ojthetiny/OpenTKL/PCB/Kicad Files/UniversalTKL.kicad_sch

## KiCad design PCB/Kicad Files/UniversalTKL.kicad_sch (2021-07-17)

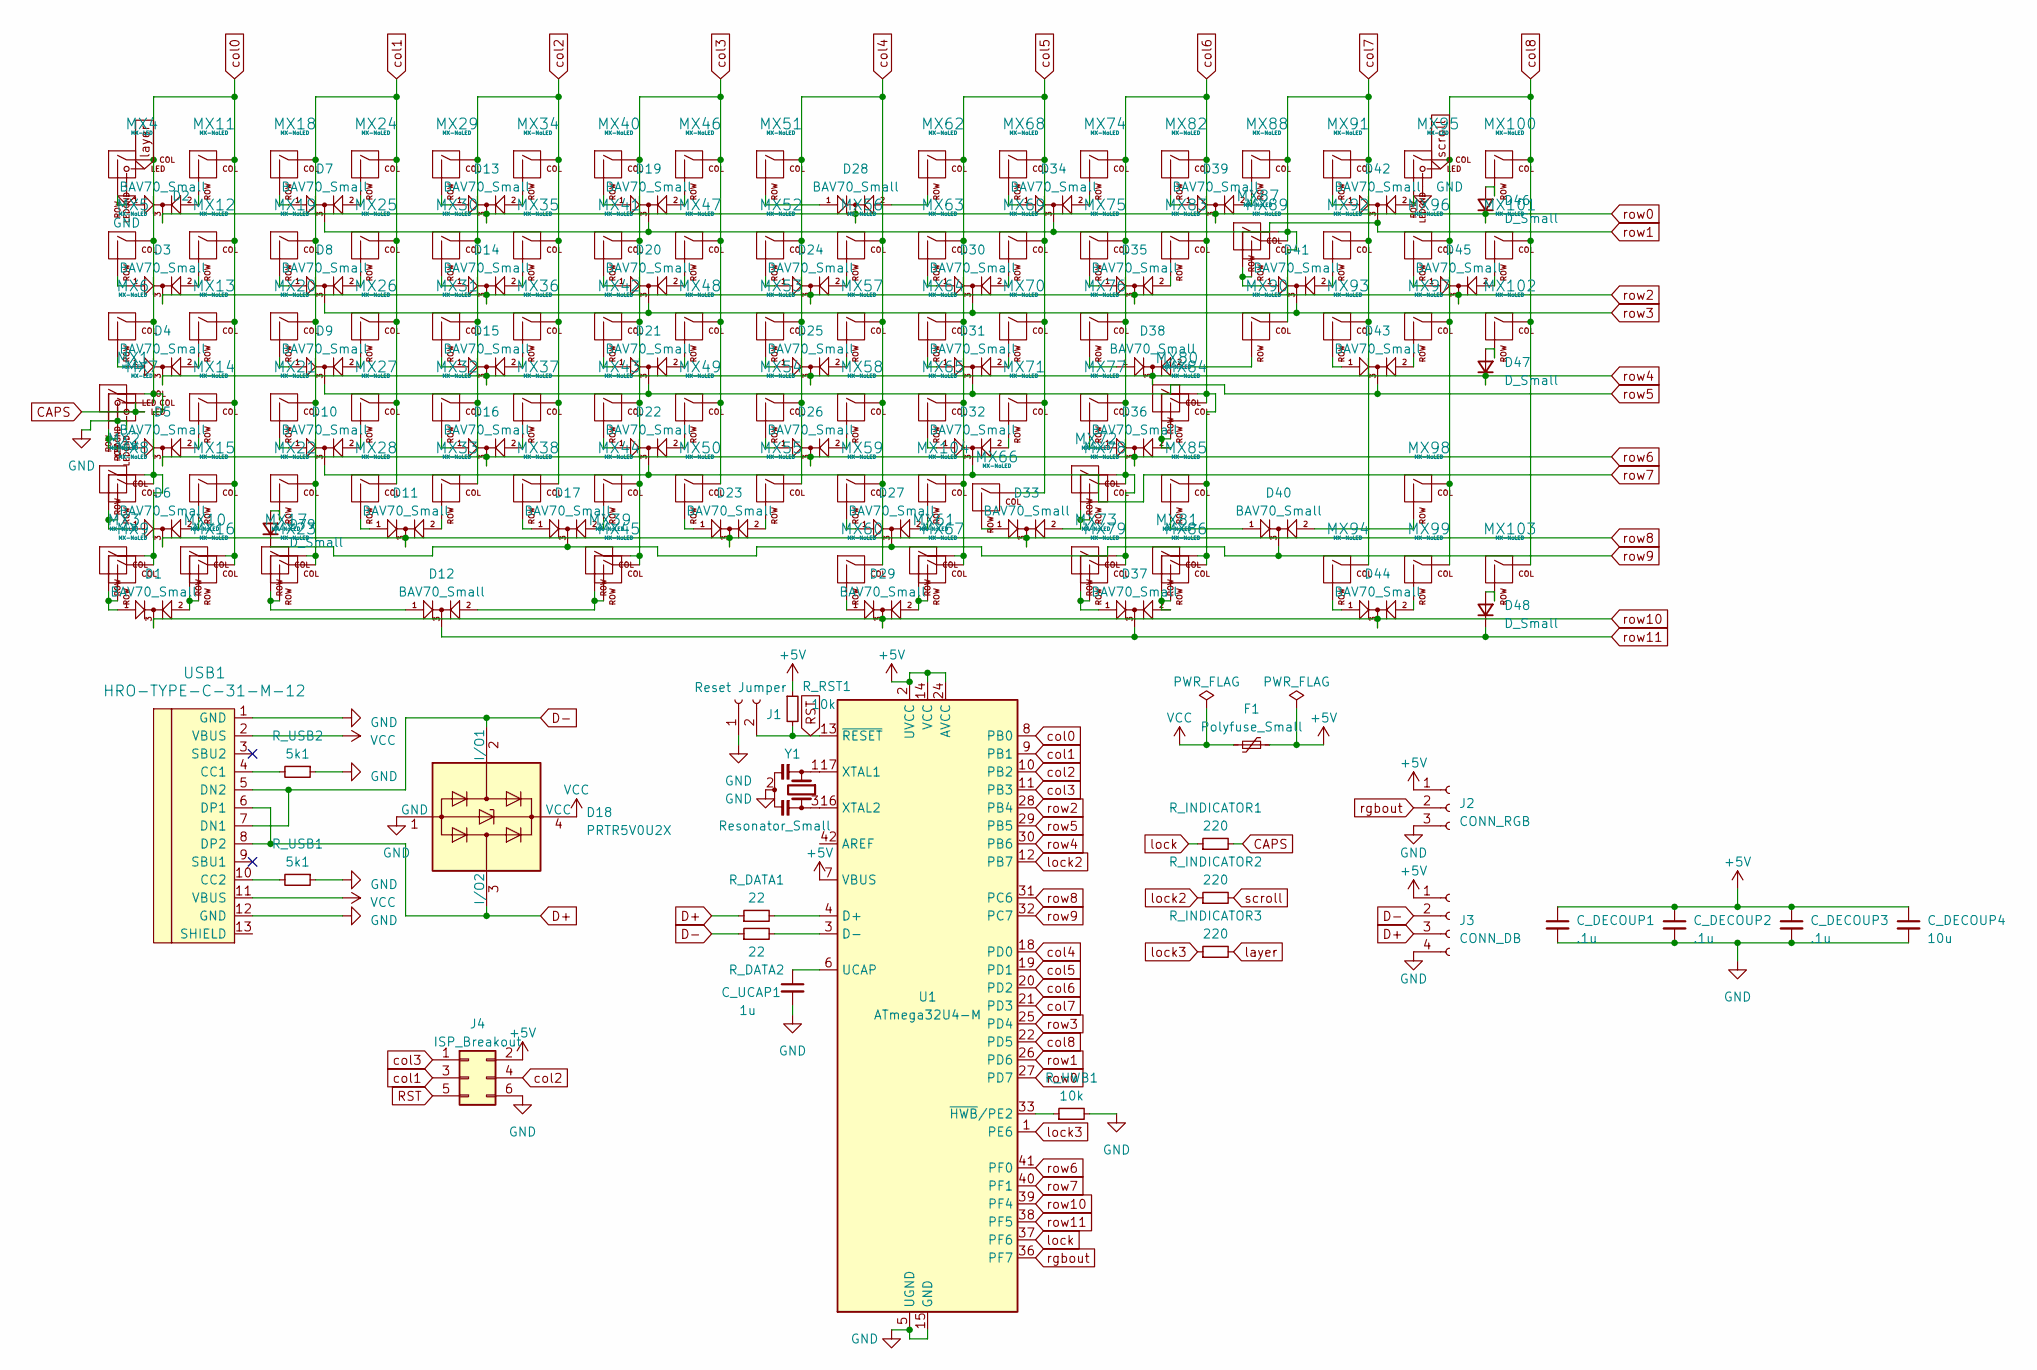
[picture p6: schematic UniversalTKL.kicad_sch]

Parts:
C_DECOUP1, C_DECOUP2, C_DECOUP3: .1u; C_0402_1005Metric
C_DECOUP4: 10u; C_0402_1005Metric
C_UCAP1: 1u; C_0402_1005Metric
D1, D2, D3, D4, D5, D6, D7, D8, D9, D10, D11, D12, D13, D14, D15, D16, D17, D19, D20, D21, D22, D23, D24, D25, D26, D27, D28, D29, D30, D31, D32, D33, D34, D35, D36, D37, D38, D39, D40, D41, D42, D43, D44, D45: BAV70_Small; SOT-23
D18: PRTR5V0U2X; SOT-143
D46, D47, D48, D79: D_Small; D_SOD-123
F1: Polyfuse_Small; Fuse_0805_2012Metric
J1: Reset Jumper; SW_SPST_TL3342
J2: CONN_RGB; PinHeader_1x03_P2.54mm_Vertical
J3: CONN_DB; JST_SH_SM04B-SRSS-TB_1x04-1MP_P1.00mm_Horizontal
J4: ISP_Breakout; PinHeader_2x03_P2.54mm_Vertical
MX1: MX-LED; MX-1.25U
MX2, MX3, MX10, MX17, MX60, MX61, MX73, MX81: MX-NoLED; MX-1.25U-NoLED
MX4, MX95: MX-LED; MX-1U
MX5, MX11, MX12, MX13, MX14, MX15, MX16, MX18, MX19, MX20, MX21, MX22, MX24, MX25, MX26, MX27, MX28, MX29, MX30, MX31, MX32, MX33, MX34, MX35, MX36, MX37, MX38, MX40, MX41, MX42, MX43, MX44, MX46, MX47, MX48, MX49, MX50, MX51, MX52, MX53, MX54, MX55, MX56, MX57, MX58, MX59, MX62, MX63, MX64, MX65, MX66, MX68, MX69, MX70, MX71, MX74, MX75, MX76, MX77, MX79, MX82, MX83, MX85, MX87, MX88, MX91, MX92, MX93, MX94, MX96, MX97, MX98, MX99, MX100, MX101, MX102, MX103, MX104: MX-NoLED; MX-1U-NoLED
MX6, MX9, MX23, MX67, MX86, MX90: MX-NoLED; MX-1.5U-NoLED
MX7: MX-LED; MX-1.75U
MX8: MX-NoLED; MX-2.25U-NoLED
MX39: MX-NoLED; MX-6.25U-ReversedStabilizers-NoLED
MX45: MX-NoLED; MX-7U-ReversedStabilizers-NoLED
MX72: MX-NoLED; MX-2.75U-NoLED
MX78: MX-NoLED; MX-1.75U_NoLED
MX80: MX-NoLED; MX-ISO-ReversedStabilizers
MX84: MX-NoLED; MX-2.25U-ReversedStabilizers-NoLED
MX89: MX-NoLED; MX-2U-NoLED
R_DATA1, R_DATA2: 22; R_0402_1005Metric
R_HWB1: 10k; R_0402_1005Metric
R_INDICATOR1, R_INDICATOR2, R_INDICATOR3: 220; R_0402_1005Metric
R_RST1: 10k; R_0402_1005Metric
R_USB1, R_USB2: 5k1; R_0402_1005Metric
U1: ATmega32U4-M; QFN-44-1EP_7x7mm_P0.5mm_EP5.2x5.2mm
USB1: HRO-TYPE-C-31-M-12; HRO-TYPE-C-31-M-12-Assembly
Y1: Resonator_Small; Resonator_SMD_Murata_CSTxExxV-3Pin_3.0x1.1mm

Connections:
+5V: C_DECOUP1.1, C_DECOUP2.1, C_DECOUP3.1, C_DECOUP4.1, F1.2, J2.1, J3.1, J4.2, R_RST1.1, U1.2 (UVCC), U1.7 (VBUS), U1.14 (VCC), U1.24 (AVCC), U1.34 (VCC), U1.44 (AVCC)
CAPS: MX1.3 (LED), MX7.3 (LED), R_INDICATOR1.2
D+: D18.3 (I/O2), J3.3, R_DATA1.1, USB1.6 (DP1), USB1.8 (DP2)
D-: D18.2 (I/O1), J3.2, R_DATA2.1, USB1.5 (DN2), USB1.7 (DN1)
GND: C_DECOUP1.2, C_DECOUP2.2, C_DECOUP3.2, C_DECOUP4.2, C_UCAP1.2, D18.1 (GND), J1.1, J2.3, J3.4, J4.6, MX1.4 (LEDGND), MX4.4 (LEDGND), MX7.4 (LEDGND), MX95.4 (LEDGND), R_HWB1.2, R_USB1.1, R_USB2.1, U1.5 (UGND), U1.15 (GND), U1.23 (GND), U1.35 (GND), U1.43 (GND), U1.45 (GND), USB1.1 (GND), USB1.12 (GND), Y1.2
unnamed: C_UCAP1.1, U1.6 (UCAP)
unnamed: D1.1 (A1), MX3.2 (ROW), MX9.2 (ROW)
unnamed: D1.2 (A2), MX10.2 (ROW), MX16.2 (ROW)
unnamed: D2.1 (A1), MX4.2 (ROW)
unnamed: D2.2 (A2), MX11.2 (ROW)
unnamed: D3.1 (A1), MX5.2 (ROW)
unnamed: D3.2 (A2), MX12.2 (ROW)
unnamed: D4.1 (A1), MX6.2 (ROW)
unnamed: D4.2 (A2), MX13.2 (ROW)
unnamed: D5.1 (A1), MX1.2 (ROW), MX7.2 (ROW)
unnamed: D5.2 (A2), MX14.2 (ROW)
unnamed: D6.1 (A1), MX2.2 (ROW), MX8.2 (ROW)
unnamed: D6.2 (A2), MX15.2 (ROW)
unnamed: D7.1 (A1), MX18.2 (ROW)
unnamed: D7.2 (A2), MX24.2 (ROW)
unnamed: D8.1 (A1), MX19.2 (ROW)
unnamed: D8.2 (A2), MX25.2 (ROW)
unnamed: D9.1 (A1), MX20.2 (ROW)
unnamed: D9.2 (A2), MX26.2 (ROW)
unnamed: D10.1 (A1), MX21.2 (ROW)
unnamed: D10.2 (A2), MX27.2 (ROW)
unnamed: D11.1 (A1), MX28.2 (ROW)
unnamed: D11.2 (A2), MX33.2 (ROW)
unnamed: D12.1 (A1), MX17.2 (ROW), MX23.2 (ROW)
unnamed: D12.2 (A2), MX39.2 (ROW), MX45.2 (ROW)
unnamed: D13.1 (A1), MX29.2 (ROW)
unnamed: D13.2 (A2), MX34.2 (ROW)
unnamed: D14.1 (A1), MX30.2 (ROW)
unnamed: D14.2 (A2), MX35.2 (ROW)
unnamed: D15.1 (A1), MX31.2 (ROW)
unnamed: D15.2 (A2), MX36.2 (ROW)
unnamed: D16.1 (A1), MX32.2 (ROW)
unnamed: D16.2 (A2), MX37.2 (ROW)
unnamed: D17.1 (A1), MX38.2 (ROW)
unnamed: D17.2 (A2), MX44.2 (ROW)
unnamed: D19.1 (A1), MX40.2 (ROW)
unnamed: D19.2 (A2), MX46.2 (ROW)
unnamed: D20.1 (A1), MX41.2 (ROW)
unnamed: D20.2 (A2), MX47.2 (ROW)
unnamed: D21.1 (A1), MX42.2 (ROW)
unnamed: D21.2 (A2), MX48.2 (ROW)
unnamed: D22.1 (A1), MX43.2 (ROW)
unnamed: D22.2 (A2), MX49.2 (ROW)
unnamed: D23.1 (A1), MX50.2 (ROW)
unnamed: D23.2 (A2), MX55.2 (ROW)
unnamed: D24.1 (A1), MX52.2 (ROW)
unnamed: D24.2 (A2), MX56.2 (ROW)
unnamed: D25.1 (A1), MX53.2 (ROW)
unnamed: D25.2 (A2), MX57.2 (ROW)
unnamed: D26.1 (A1), MX54.2 (ROW)
unnamed: D26.2 (A2), MX58.2 (ROW)
unnamed: D27.1 (A1), MX59.2 (ROW)
unnamed: D27.2 (A2), MX104.2 (ROW)
unnamed: D28.1 (A1), MX51.2 (ROW)
unnamed: D28.2 (A2), MX62.2 (ROW)
unnamed: D29.1 (A1), MX60.2 (ROW)
unnamed: D29.2 (A2), MX61.2 (ROW), MX67.2 (ROW)
unnamed: D30.1 (A1), MX63.2 (ROW)
unnamed: D30.2 (A2), MX69.2 (ROW)
unnamed: D31.1 (A1), MX64.2 (ROW)
unnamed: D31.2 (A2), MX70.2 (ROW)
unnamed: D32.1 (A1), MX65.2 (ROW)
unnamed: D32.2 (A2), MX71.2 (ROW)
unnamed: D33.1 (A1), MX66.2 (ROW)
unnamed: D33.2 (A2), MX72.2 (ROW), MX78.2 (ROW)
unnamed: D34.1 (A1), MX68.2 (ROW)
unnamed: D34.2 (A2), MX74.2 (ROW)
unnamed: D35.1 (A1), MX75.2 (ROW)
unnamed: D35.2 (A2), MX83.2 (ROW)
unnamed: D36.1 (A1), MX77.2 (ROW)
unnamed: D36.2 (A2), MX80.2 (ROW), MX84.2 (ROW)
unnamed: D37.1 (A1), MX73.2 (ROW), MX79.2 (ROW)
unnamed: D37.2 (A2), MX81.2 (ROW), MX86.2 (ROW)
unnamed: D38.1 (A1), MX76.2 (ROW)
unnamed: D38.2 (A2), MX90.2 (ROW)
unnamed: D39.1 (A1), MX82.2 (ROW)
unnamed: D39.2 (A2), MX88.2 (ROW)
unnamed: D40.1 (A1), MX85.2 (ROW)
unnamed: D40.2 (A2), MX98.2 (ROW)
unnamed: D41.1 (A1), MX87.2 (ROW), MX89.2 (ROW)
unnamed: D41.2 (A2), MX92.2 (ROW)
unnamed: D42.1 (A1), MX91.2 (ROW)
unnamed: D42.2 (A2), MX95.2 (ROW)
unnamed: D43.1 (A1), MX93.2 (ROW)
unnamed: D43.2 (A2), MX97.2 (ROW)
unnamed: D44.1 (A1), MX94.2 (ROW)
unnamed: D44.2 (A2), MX99.2 (ROW)
unnamed: D45.1 (A1), MX96.2 (ROW)
unnamed: D45.2 (A2), MX101.2 (ROW)
unnamed: D46.2 (A), MX100.2 (ROW)
unnamed: D47.2 (A), MX102.2 (ROW)
unnamed: D48.2 (A), MX103.2 (ROW)
unnamed: D79.2 (A), MX22.2 (ROW)
unnamed: R_DATA1.2, U1.4 (D+)
unnamed: R_DATA2.2, U1.3 (D-)
unnamed: R_HWB1.1, U1.33 (~HWB/PE2)
unnamed: R_USB1.2, USB1.10 (CC2)
unnamed: R_USB2.2, USB1.4 (CC1)
unnamed: U1.16 (XTAL2), Y1.3
unnamed: U1.17 (XTAL1), Y1.1
RST: J1.2, J4.5, R_RST1.2, U1.13 (~RESET)
VCC: D18.4 (VCC), F1.1, USB1.2 (VBUS), USB1.11 (VBUS)
col0: MX1.1 (COL), MX2.1 (COL), MX3.1 (COL), MX4.1 (COL), MX5.1 (COL), MX6.1 (COL), MX7.1 (COL), MX8.1 (COL), MX9.1 (COL), MX10.1 (COL), MX11.1 (COL), MX12.1 (COL), MX13.1 (COL), MX14.1 (COL), MX15.1 (COL), MX16.1 (COL), U1.8 (PB0)
col1: J4.3, MX17.1 (COL), MX18.1 (COL), MX19.1 (COL), MX20.1 (COL), MX21.1 (COL), MX22.1 (COL), MX23.1 (COL), MX24.1 (COL), MX25.1 (COL), MX26.1 (COL), MX27.1 (COL), MX28.1 (COL), U1.9 (PB1)
col2: J4.4, MX29.1 (COL), MX30.1 (COL), MX31.1 (COL), MX32.1 (COL), MX33.1 (COL), MX34.1 (COL), MX35.1 (COL), MX36.1 (COL), MX37.1 (COL), MX38.1 (COL), U1.10 (PB2)
col3: J4.1, MX39.1 (COL), MX40.1 (COL), MX41.1 (COL), MX42.1 (COL), MX43.1 (COL), MX44.1 (COL), MX45.1 (COL), MX46.1 (COL), MX47.1 (COL), MX48.1 (COL), MX49.1 (COL), MX50.1 (COL), U1.11 (PB3)
col4: MX51.1 (COL), MX52.1 (COL), MX53.1 (COL), MX54.1 (COL), MX55.1 (COL), MX56.1 (COL), MX57.1 (COL), MX58.1 (COL), MX59.1 (COL), MX60.1 (COL), U1.18 (PD0)
col5: MX61.1 (COL), MX62.1 (COL), MX63.1 (COL), MX64.1 (COL), MX65.1 (COL), MX66.1 (COL), MX67.1 (COL), MX68.1 (COL), MX69.1 (COL), MX70.1 (COL), MX71.1 (COL), MX104.1 (COL), U1.19 (PD1)
col6: MX72.1 (COL), MX73.1 (COL), MX74.1 (COL), MX75.1 (COL), MX76.1 (COL), MX77.1 (COL), MX78.1 (COL), MX79.1 (COL), MX80.1 (COL), MX81.1 (COL), MX82.1 (COL), MX83.1 (COL), MX84.1 (COL), MX85.1 (COL), MX86.1 (COL), U1.20 (PD2)
col7: MX87.1 (COL), MX88.1 (COL), MX89.1 (COL), MX90.1 (COL), MX91.1 (COL), MX92.1 (COL), MX93.1 (COL), MX94.1 (COL), U1.21 (PD3)
col8: MX95.1 (COL), MX96.1 (COL), MX97.1 (COL), MX98.1 (COL), MX99.1 (COL), MX100.1 (COL), MX101.1 (COL), MX102.1 (COL), MX103.1 (COL), U1.22 (PD5)
layer: MX4.3 (LED), R_INDICATOR3.2
lock: R_INDICATOR1.1, U1.37 (PF6)
lock2: R_INDICATOR2.1, U1.12 (PB7)
lock3: R_INDICATOR3.1, U1.1 (PE6)
rgbout: J2.2, U1.36 (PF7)
row0: D2.3 (K), D13.3 (K), D28.3 (K), D39.3 (K), D46.1 (K), U1.27 (PD7)
row1: D7.3 (K), D19.3 (K), D34.3 (K), D42.3 (K), U1.26 (PD6)
row2: D3.3 (K), D14.3 (K), D24.3 (K), D35.3 (K), D45.3 (K), U1.28 (PB4)
row3: D8.3 (K), D20.3 (K), D30.3 (K), D41.3 (K), U1.25 (PD4)
row4: D4.3 (K), D15.3 (K), D25.3 (K), D38.3 (K), D47.1 (K), U1.30 (PB6)
row5: D9.3 (K), D21.3 (K), D31.3 (K), D43.3 (K), U1.29 (PB5)
row6: D5.3 (K), D16.3 (K), D26.3 (K), D36.3 (K), U1.41 (PF0)
row7: D10.3 (K), D22.3 (K), D32.3 (K), U1.40 (PF1)
row8: D6.3 (K), D11.3 (K), D23.3 (K), D33.3 (K), U1.31 (PC6)
row9: D17.3 (K), D27.3 (K), D40.3 (K), D79.1 (K), U1.32 (PC7)
row10: D1.3 (K), D29.3 (K), D44.3 (K), U1.39 (PF4)
row11: D12.3 (K), D37.3 (K), D48.1 (K), U1.38 (PF5)
scroll: MX95.3 (LED), R_INDICATOR2.2
